sujaldavda/Spider-Like-Quadruped-/robot_description/meshes/quadrapod reddit - servo horn-12.STL

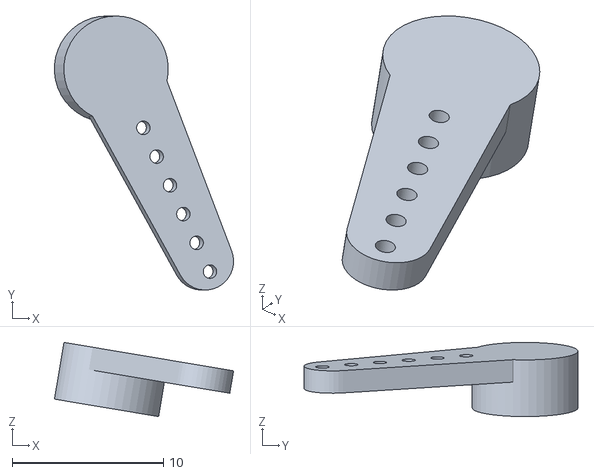
[picture p15: CAD file, 2026-09-20]
robot_description/meshes/quadrapod reddit - servo horn-12.STL
11.8 x 18.1 x 4.90
