sujaldavda/Spider-Like-Quadruped-/robot_description/meshes/quadrapod reddit - Servo_motor.step-5.STL

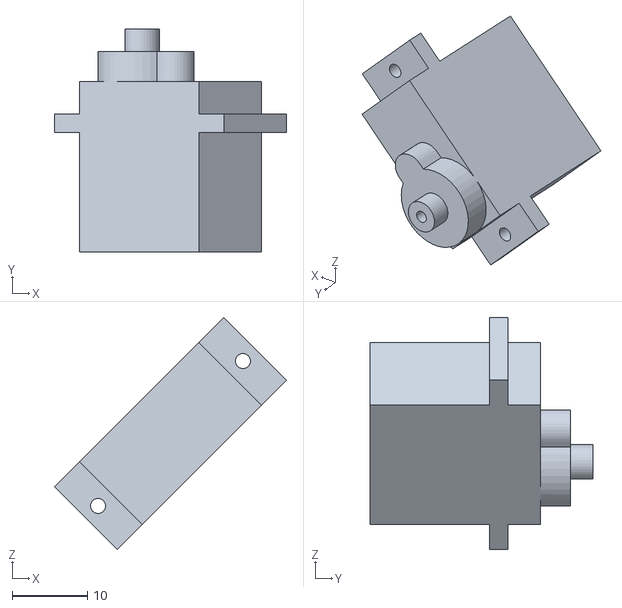
[picture p16: CAD file, 2026-09-20]
robot_description/meshes/quadrapod reddit - Servo_motor.step-5.STL
30.9 x 29.7 x 30.9
