sujaldavda/Spider-Like-Quadruped-/robot_description/meshes/quadrapod reddit - mid clamp redesign-1.STL

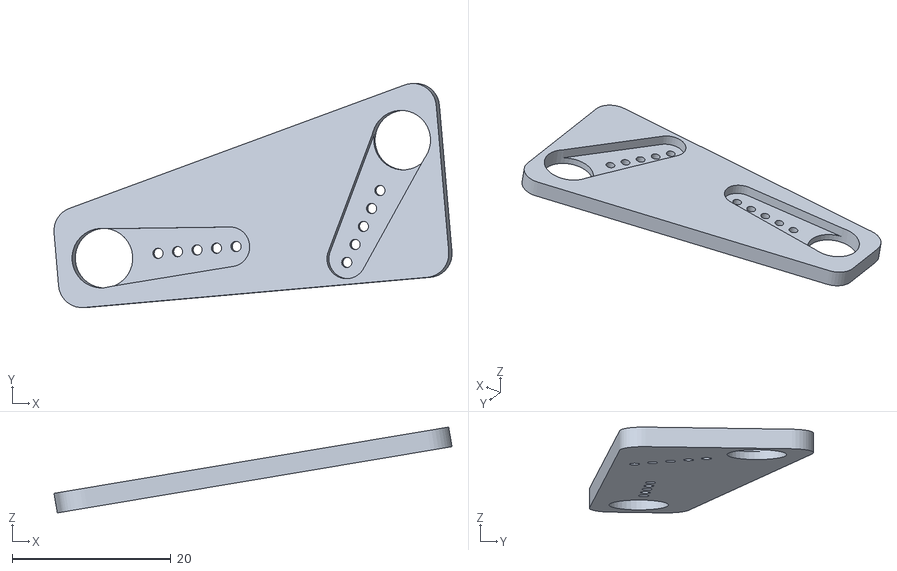
[picture p17: CAD file, 2026-09-20]
robot_description/meshes/quadrapod reddit - mid clamp redesign-1.STL
50.1 x 28.2 x 10.8
