sujaldavda/Spider-Like-Quadruped-/robot_description/meshes/quadrapod reddit - base 5.0 remake-1.STL

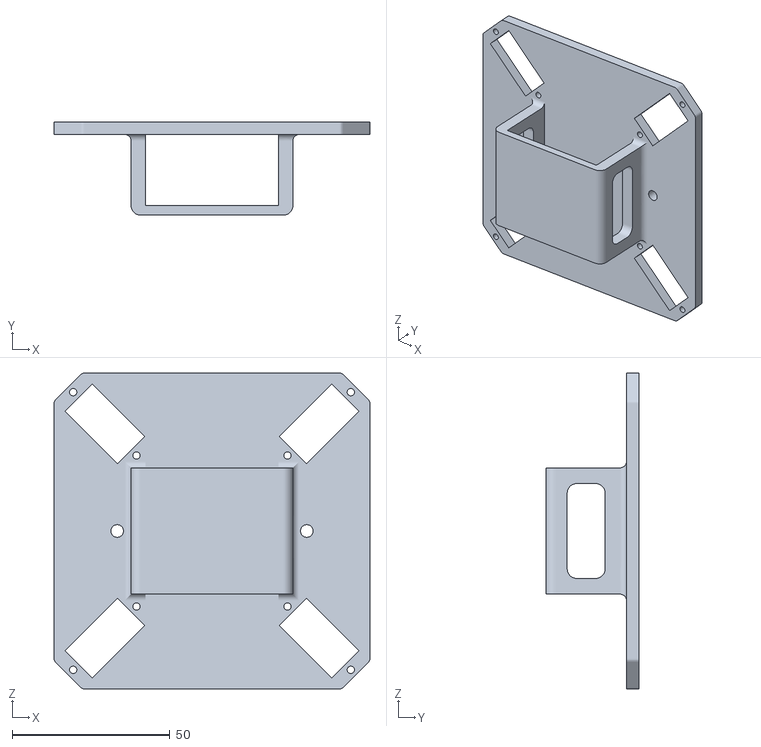
[picture p18: CAD file, 2026-09-20]
robot_description/meshes/quadrapod reddit - base 5.0 remake-1.STL
100.0 x 29.5 x 100.0
