sujaldavda/Spider-Like-Quadruped-/robot_description/meshes/quadrapod reddit - servo horn-6.STL

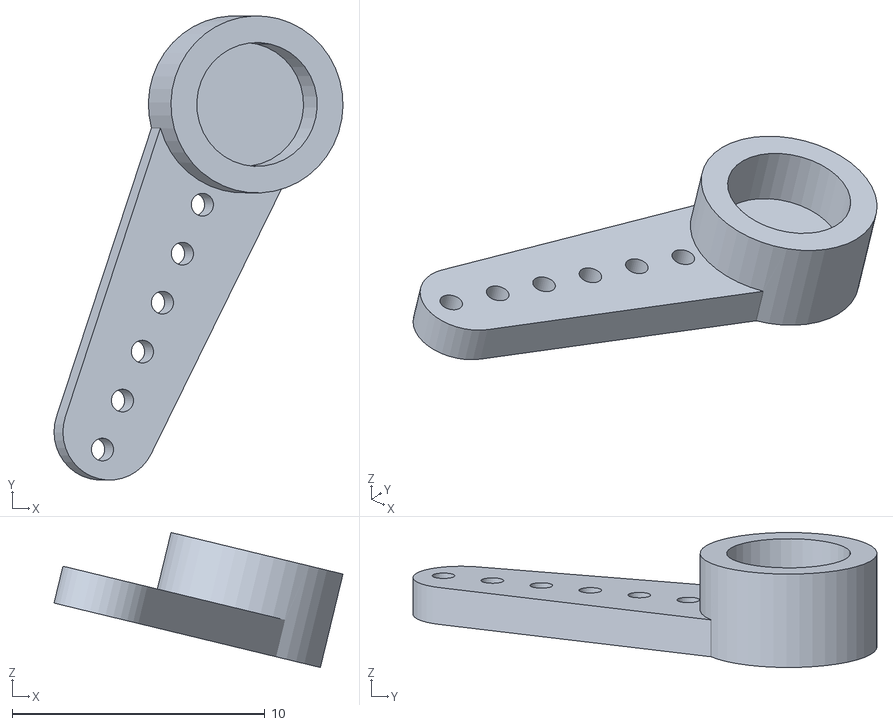
[picture p19: CAD file, 2026-09-20]
robot_description/meshes/quadrapod reddit - servo horn-6.STL
11.4 x 18.3 x 5.34
