sujaldavda/Spider-Like-Quadruped-/robot_description/meshes/quadrapod reddit - Mirrormid clamp redesign---------------------2.STL

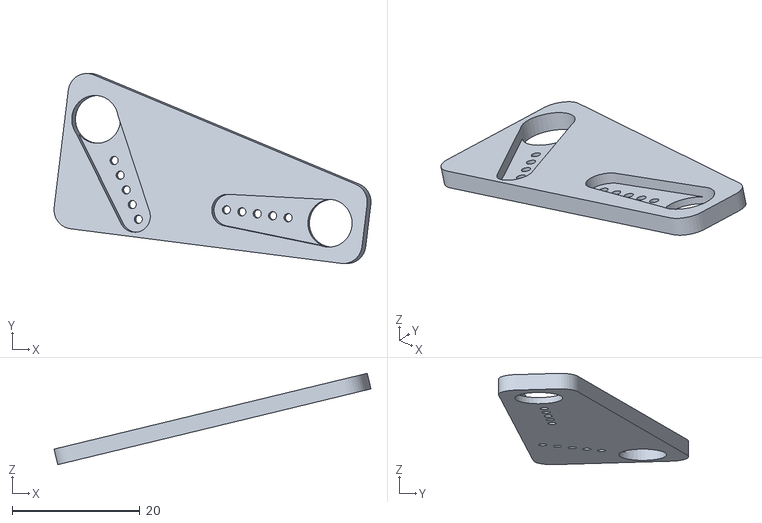
[picture p20: CAD file, 2026-09-20]
robot_description/meshes/quadrapod reddit - Mirrormid clamp redesign---------------------2.STL
49.7 x 29.8 x 14.3
