sujaldavda/Spider-Like-Quadruped-/robot_description/meshes/quadrapod reddit - Servo_motor.step-9.STL

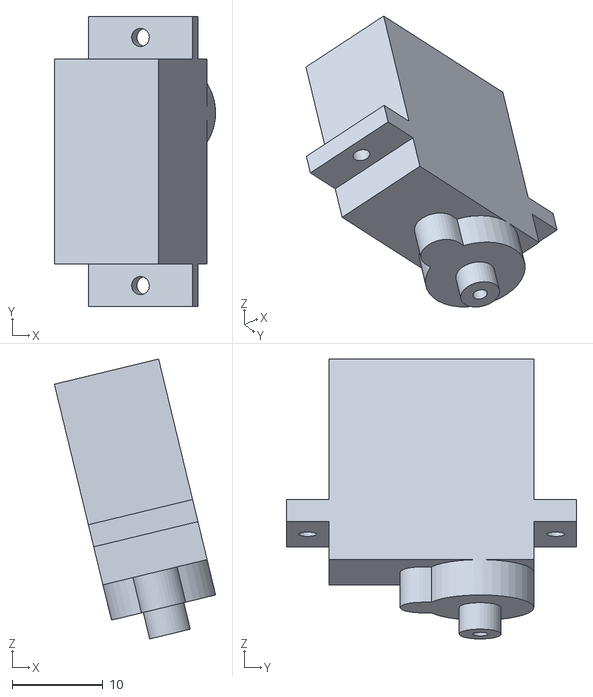
[picture p21: CAD file, 2026-09-20]
robot_description/meshes/quadrapod reddit - Servo_motor.step-9.STL
17.7 x 31.9 x 30.8
