sujaldavda/Spider-Like-Quadruped-/robot_description/meshes/quadrapod reddit - tibia tip-3.STL

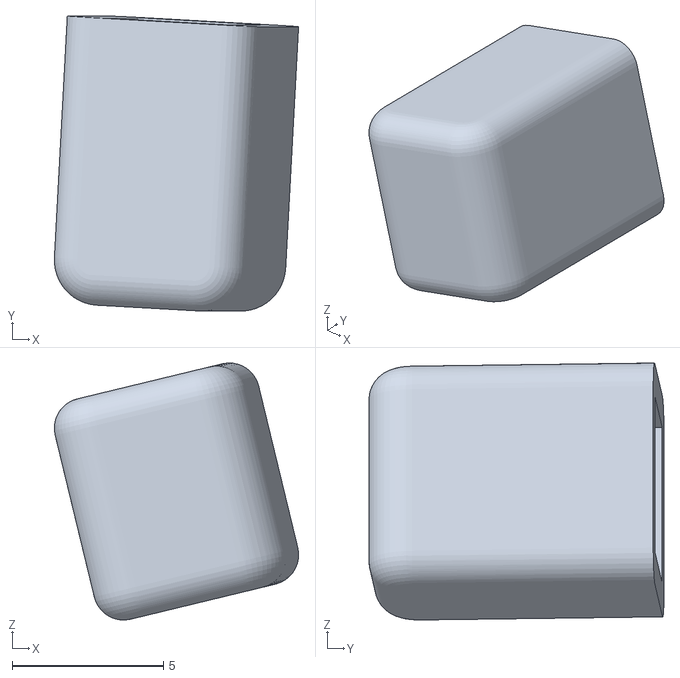
[picture p22: CAD file, 2026-09-20]
robot_description/meshes/quadrapod reddit - tibia tip-3.STL
8.08 x 9.76 x 8.50
