sujaldavda/Spider-Like-Quadruped-/robot_description/meshes/quadrapod reddit - tibia tip-1.STL

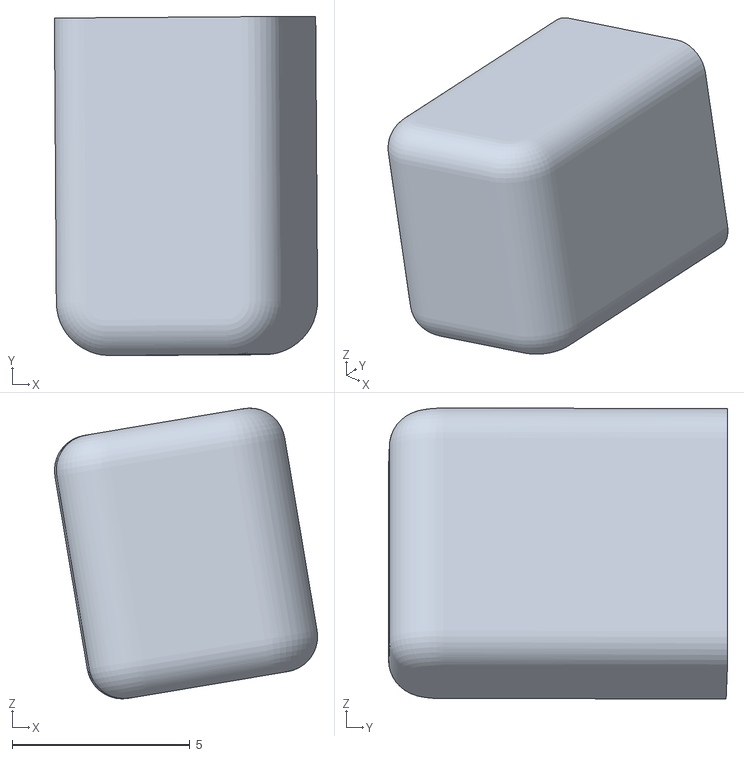
[picture p23: CAD file, 2026-09-20]
robot_description/meshes/quadrapod reddit - tibia tip-1.STL
7.40 x 9.53 x 8.18
