sujaldavda/Spider-Like-Quadruped-/robot_description/meshes/quadrapod reddit - servo horn-4.STL

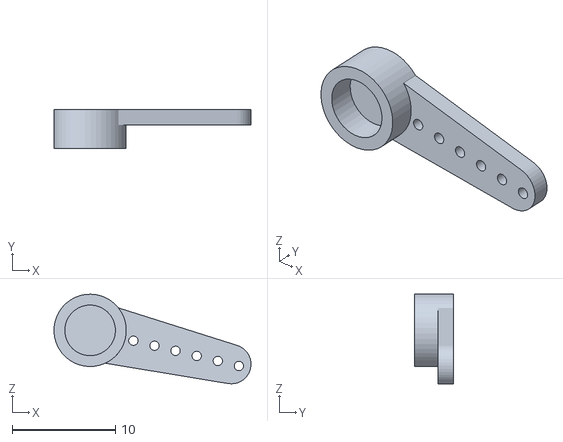
[picture p24: CAD file, 2026-09-20]
robot_description/meshes/quadrapod reddit - servo horn-4.STL
19.1 x 3.80 x 8.67
