sujaldavda/Spider-Like-Quadruped-/robot_description/meshes/quadrapod reddit - tibia RD-4.STL

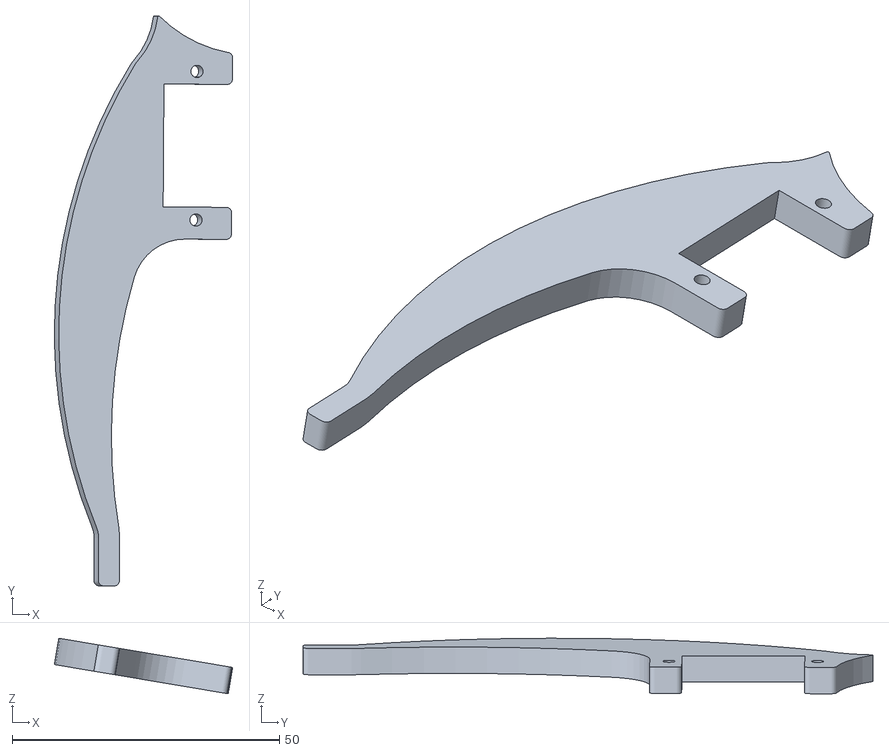
[picture p25: CAD file, 2026-09-20]
robot_description/meshes/quadrapod reddit - tibia RD-4.STL
33.4 x 106.7 x 10.4
