sujaldavda/Spider-Like-Quadruped-/robot_description/meshes/quadrapod reddit - servo horn-5.STL

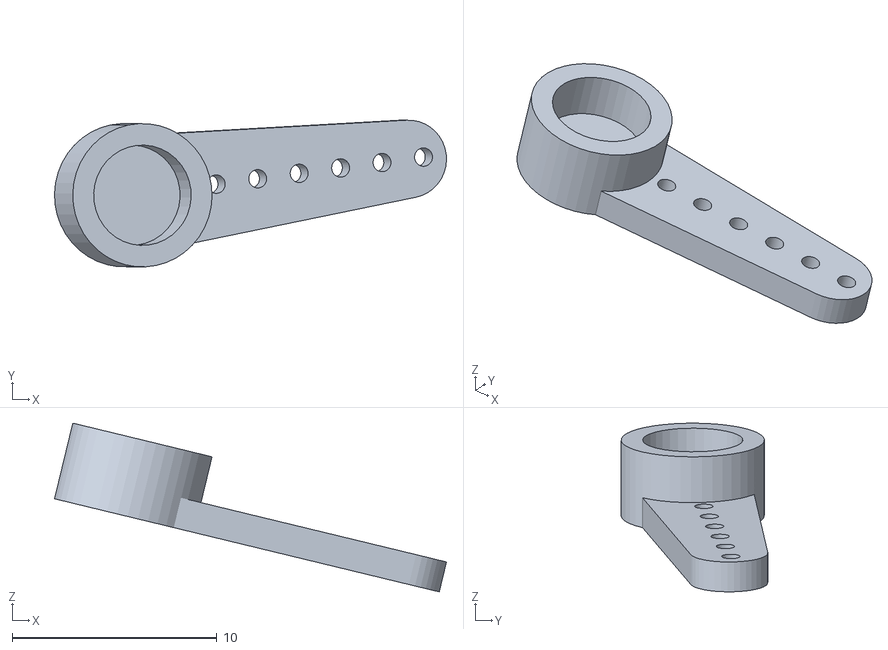
[picture p26: CAD file, 2026-09-20]
robot_description/meshes/quadrapod reddit - servo horn-5.STL
19.1 x 7.16 x 8.24
