sujaldavda/Spider-Like-Quadruped-/robot_description/meshes/quadrapod reddit - Mirrorclamp 1 redesigned-2.STL

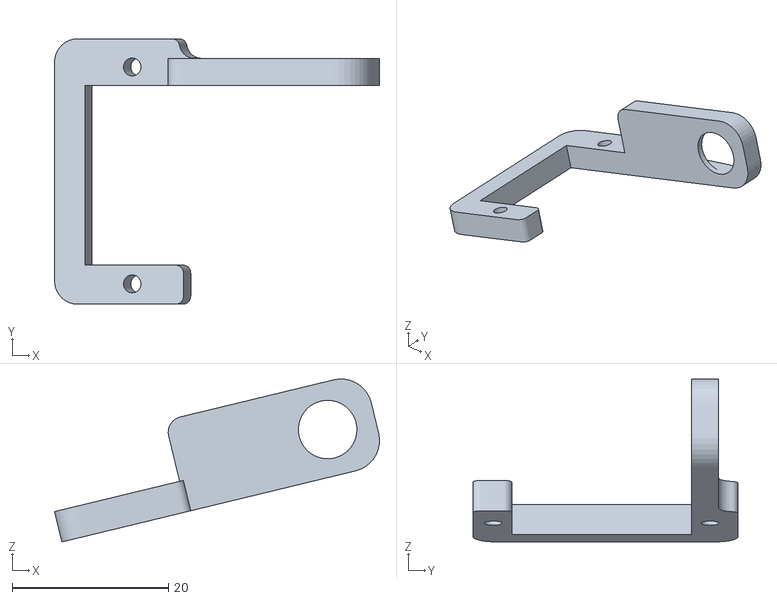
[picture p27: CAD file, 2026-09-20]
robot_description/meshes/quadrapod reddit - Mirrorclamp 1 redesigned-2.STL
41.7 x 34.0 x 20.9
